enenflash/YounglingSlayer/mechanical design/metro/fusion.png

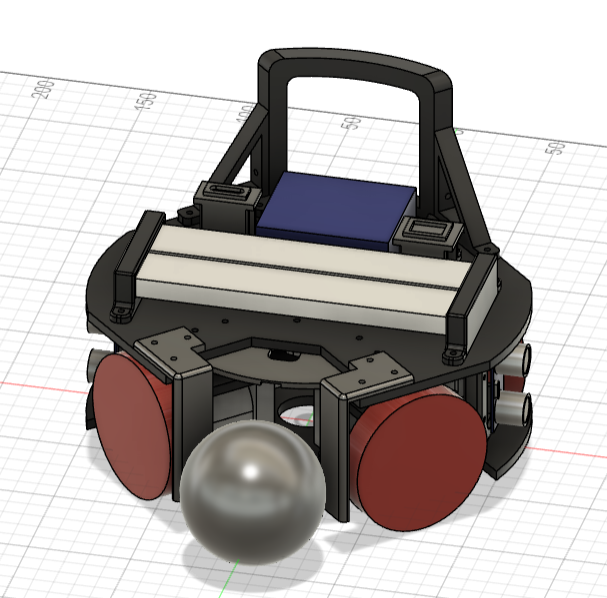
mechanical design/metro/fusion.png
