enenflash/YounglingSlayer/mechanical design/metro/L2_motor_mounts.png

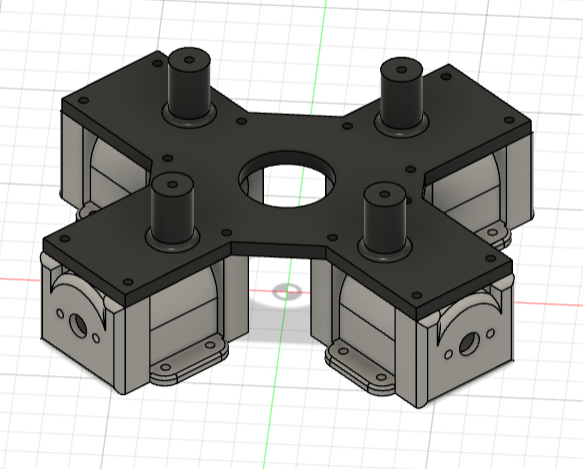
mechanical design/metro/L2_motor_mounts.png
