enenflash/YounglingSlayer/mechanical design/metro/L3_holes.png

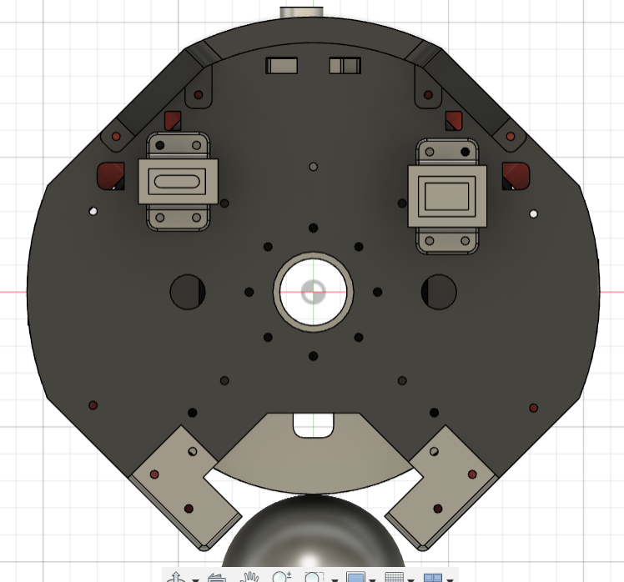
mechanical design/metro/L3_holes.png
