enenflash/YounglingSlayer/mechanical design/metro/layout.png

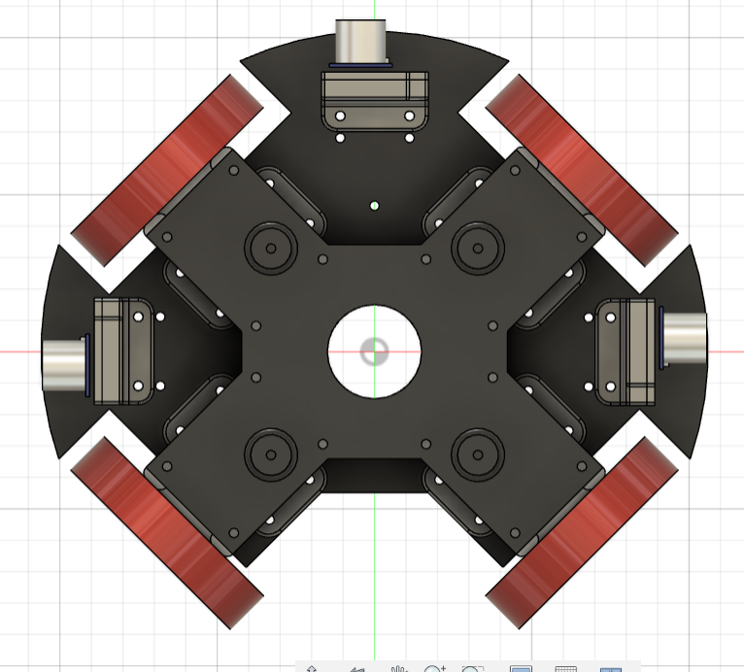
mechanical design/metro/layout.png
