enenflash/YounglingSlayer/mechanical design/metro/planning.png

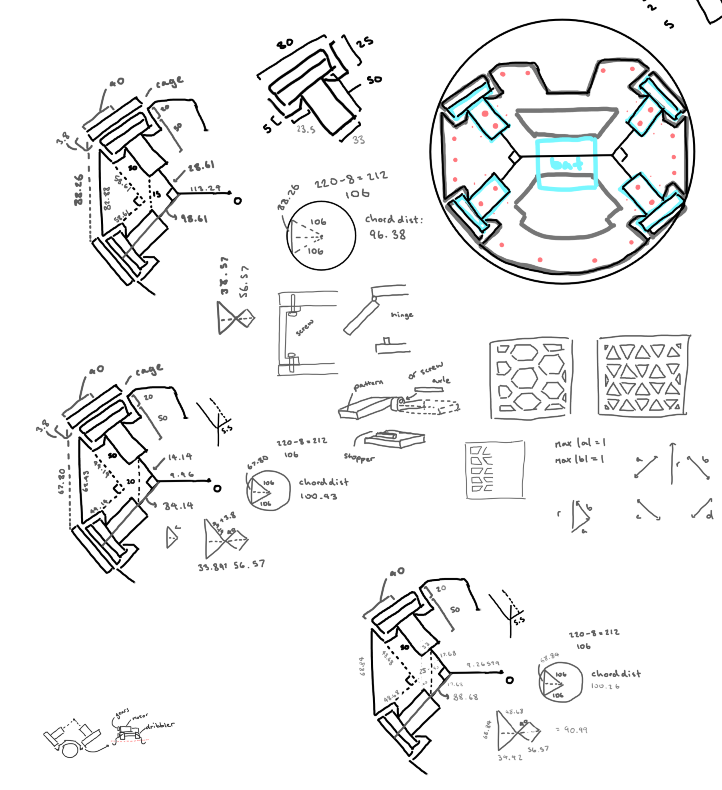
mechanical design/metro/planning.png
