enenflash/YounglingSlayer/mechanical design/metro/wheel/fusion.png

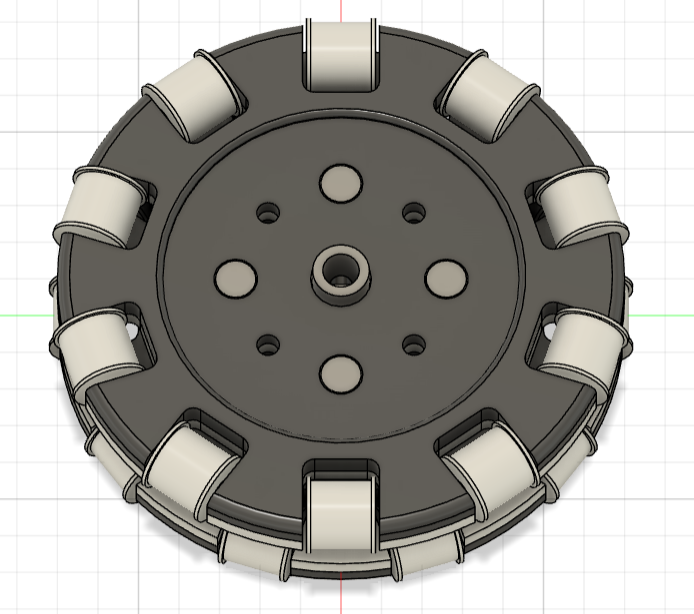
mechanical design/metro/wheel/fusion.png
