enenflash/YounglingSlayer/mechanical design/nationals/fusion.png

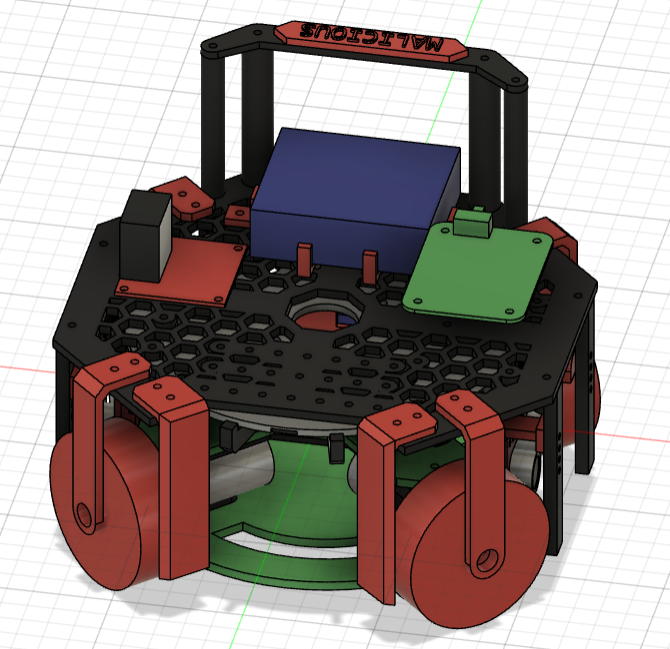
mechanical design/nationals/fusion.png
