enenflash/YounglingSlayer/mechanical design/nationals/wheel_guard.png

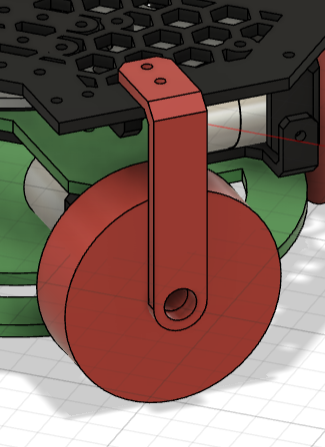
mechanical design/nationals/wheel_guard.png
