enenflash/YounglingSlayer/mechanical design/state/bottom_view.png

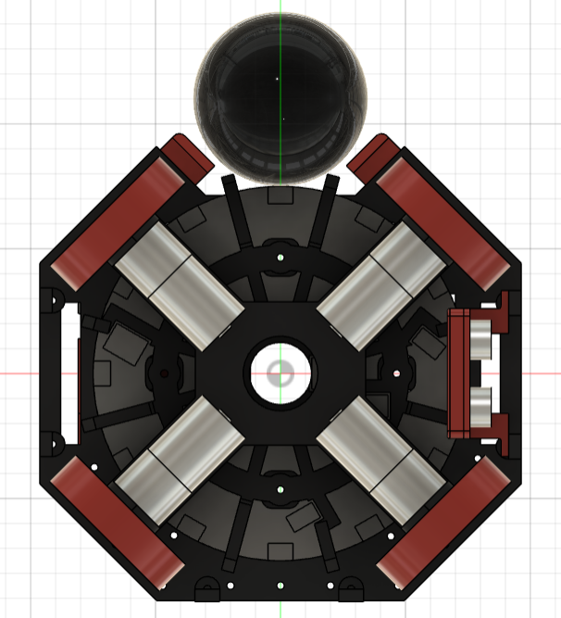
mechanical design/state/bottom_view.png
