enenflash/YounglingSlayer/mechanical design/state/fusion.png

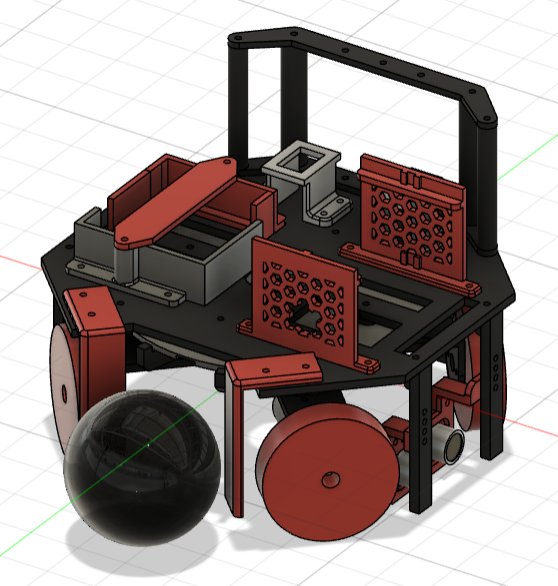
mechanical design/state/fusion.png
