enenflash/YounglingSlayer/mechanical design/state/IR_mount.png

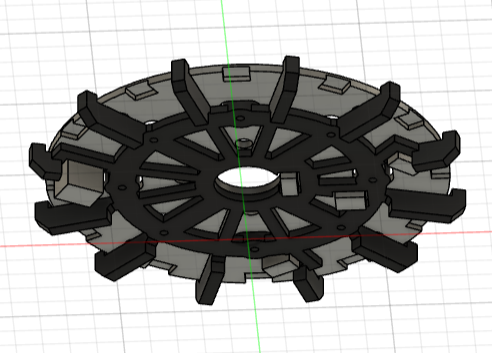
mechanical design/state/IR_mount.png
