enenflash/YounglingSlayer/mechanical design/state/L2-motors.png

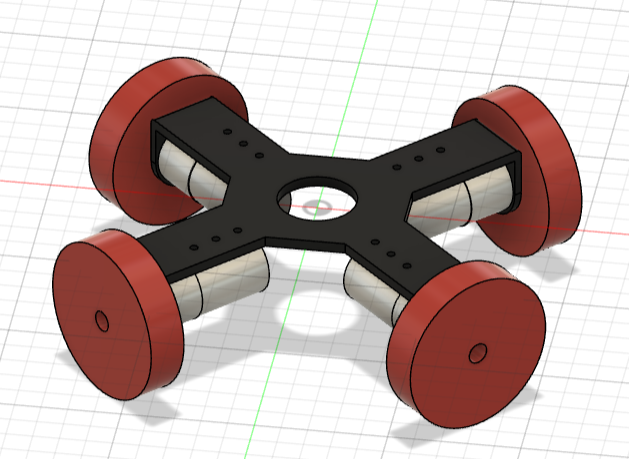
mechanical design/state/L2-motors.png
