enenflash/YounglingSlayer/mechanical design/state/structure.png

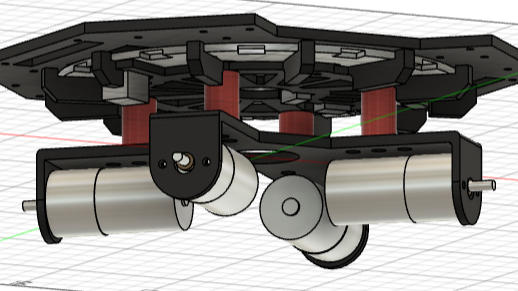
mechanical design/state/structure.png
