enenflash/YounglingSlayer/pcbs/line_sensor-26-08/design.png

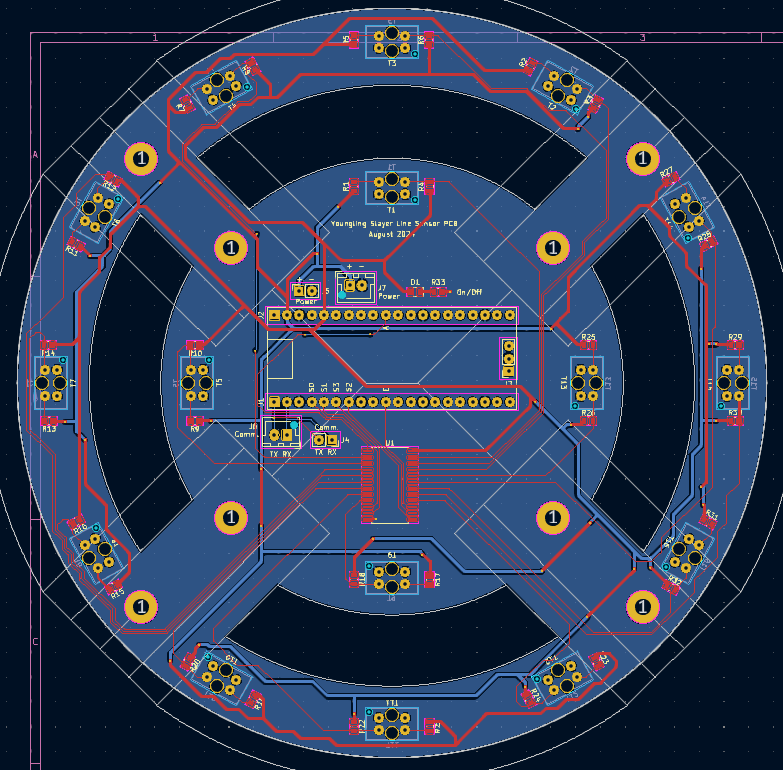
pcbs/line_sensor-26-08/design.png
