enenflash/YounglingSlayer/pcbs/line_sensor-26-08/down_3d_view.png

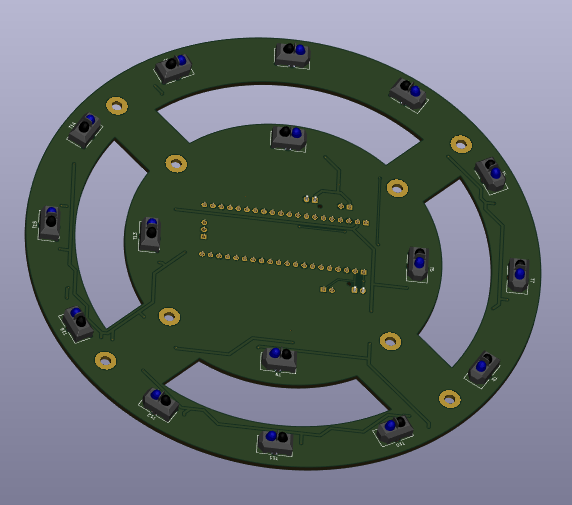
pcbs/line_sensor-26-08/down_3d_view.png
