enenflash/YounglingSlayer/pcbs/line_sensor-26-08/top_3d_view.png

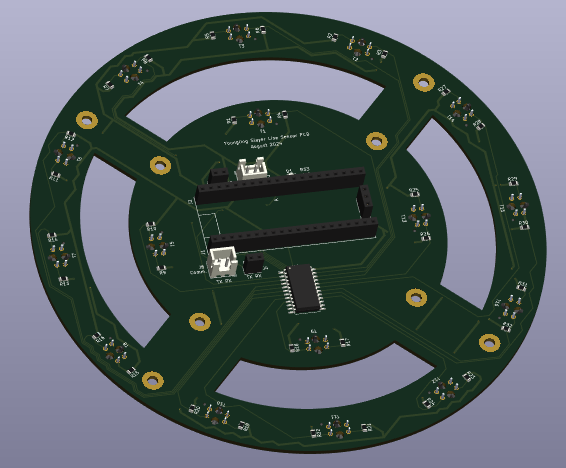
pcbs/line_sensor-26-08/top_3d_view.png
