enenflash/YounglingSlayer/pcbs/main_pcb_bottom/3d_view.png

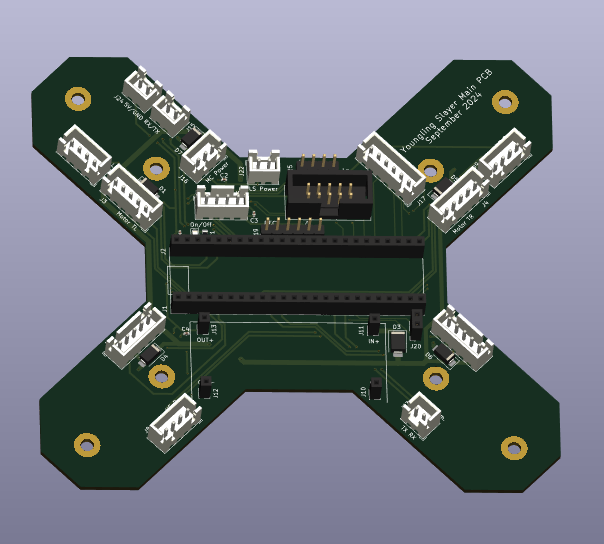
pcbs/main_pcb_bottom/3d_view.png
