enenflash/YounglingSlayer/pcbs/main_pcb_bottom/design.png

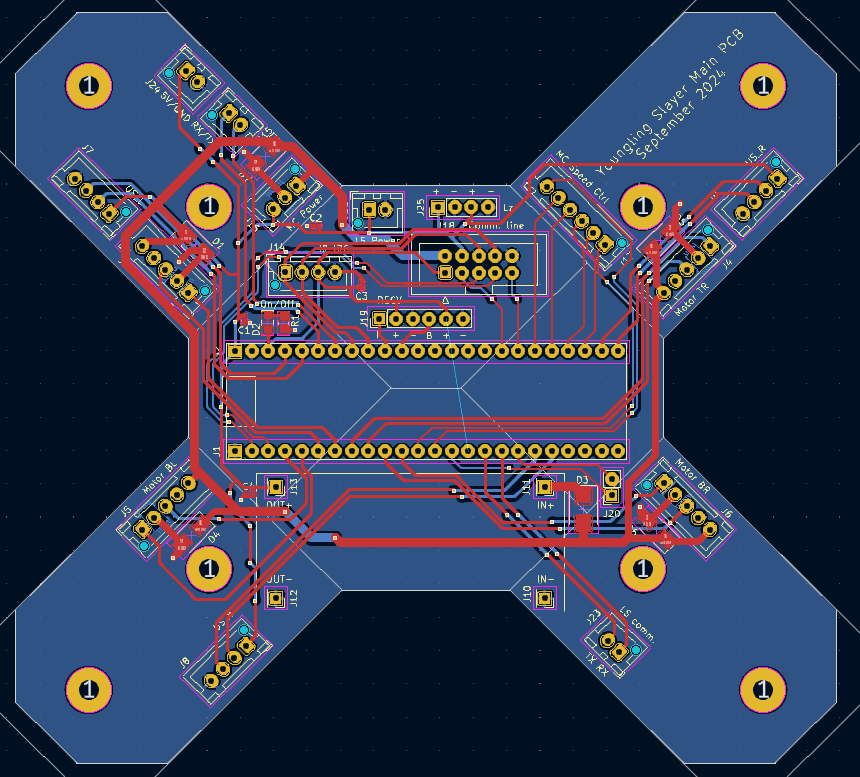
pcbs/main_pcb_bottom/design.png
