enenflash/YounglingSlayer/pcbs/main_pcb_bottom/schematic.png

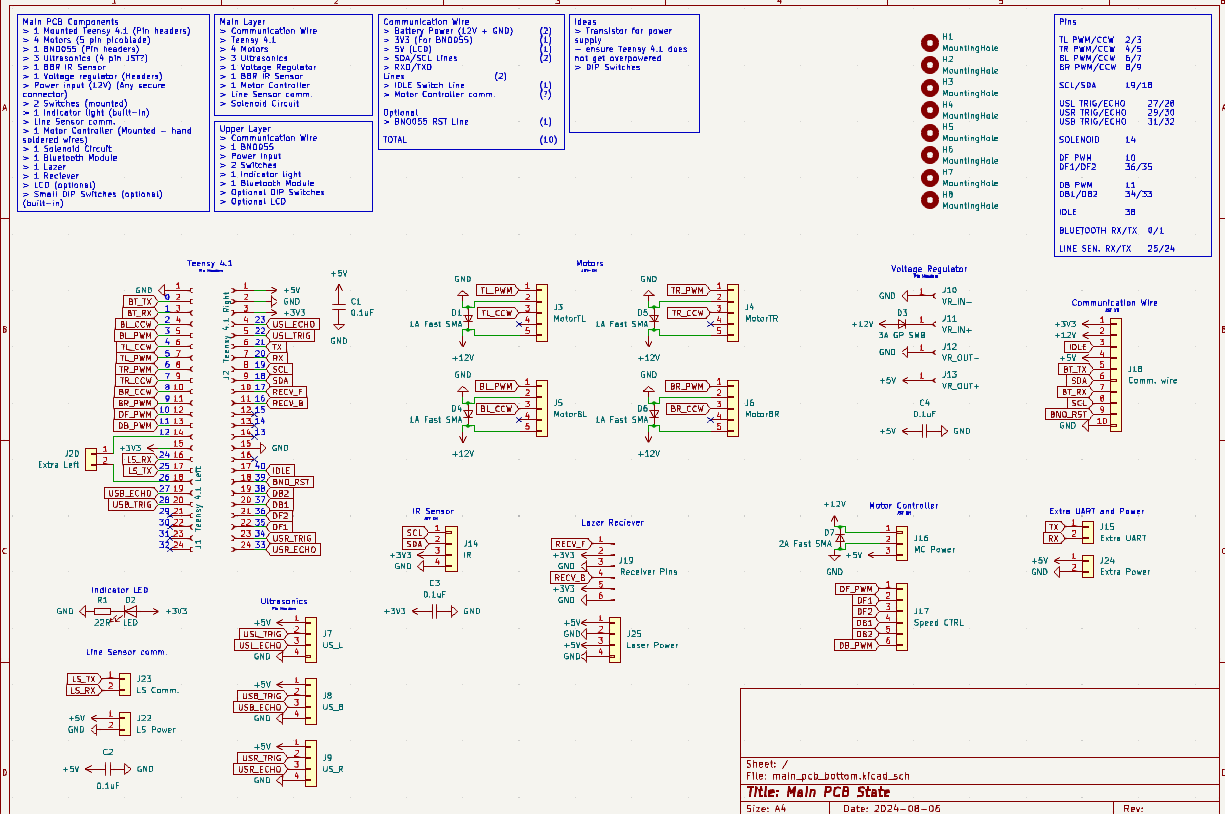
pcbs/main_pcb_bottom/schematic.png
