enenflash/YounglingSlayer/pcbs/main_pcb_top/3d_view.png

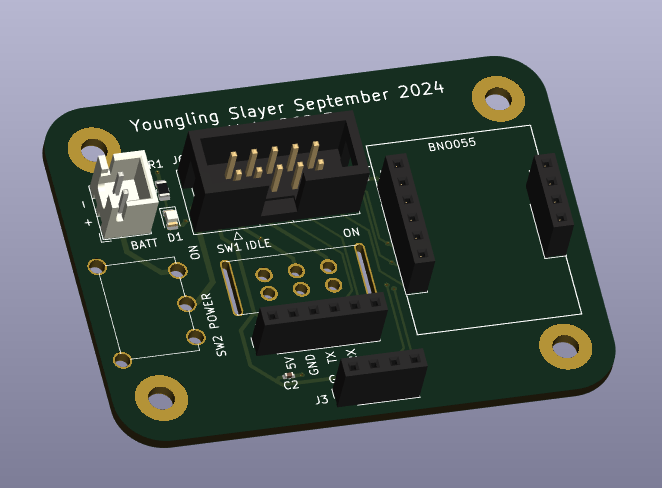
pcbs/main_pcb_top/3d_view.png
