enenflash/YounglingSlayer/pcbs/main_pcb_top/design.png

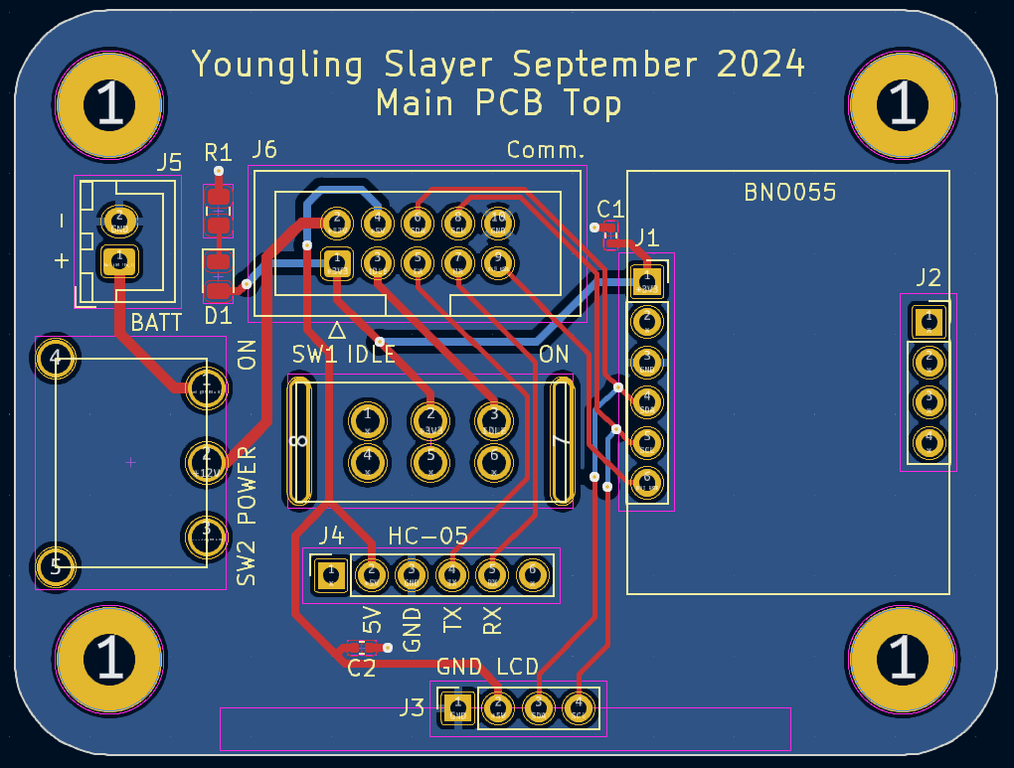
pcbs/main_pcb_top/design.png
