enenflash/YounglingSlayer/pcbs/main_pcb_top/schematic.png

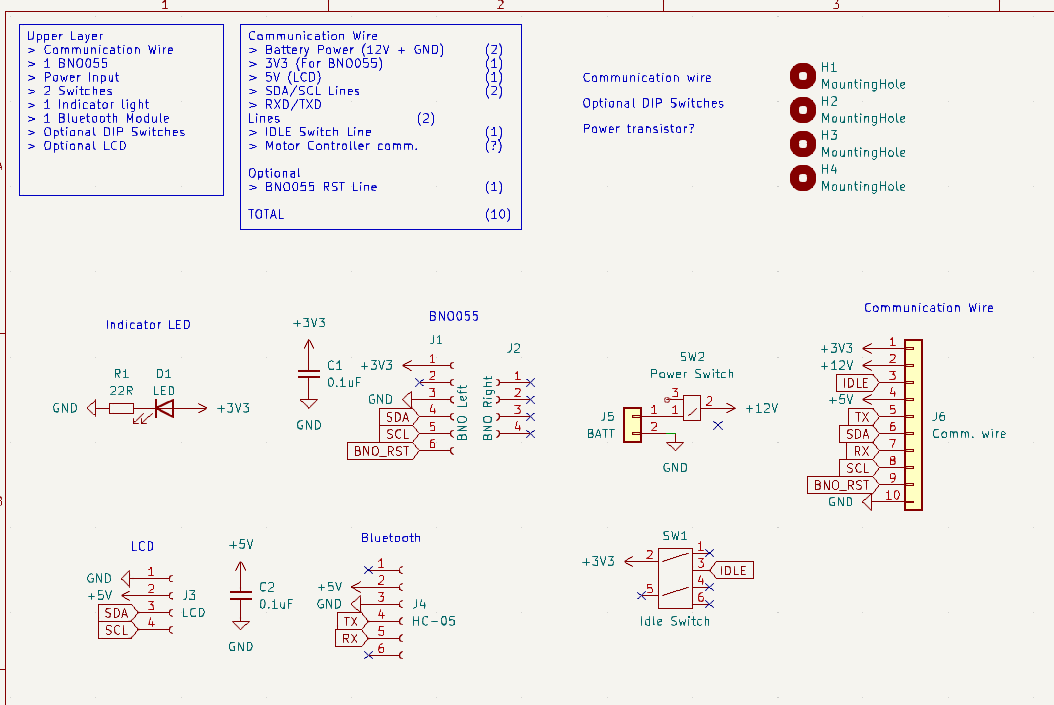
pcbs/main_pcb_top/schematic.png
