enenflash/YounglingSlayer/code-2024/nationals/RobotClass-goaltilt-1-10/RobotClass-goaltilt-1-10.ino

#include <iostream>
#include <array>
#include <map>
#include <algorithm>

#include <Wire.h>
#include <Adafruit_Sensor.h>
#include <Adafruit_BNO055.h>
#include <utility/imumaths.h>
#include <SoftwareSerial.h>

using namespace std;

// Motor Pins
#define TL_PWM 5
#define TL_DIR 4
#define TR_PWM 6
#define TR_DIR 7
#define BL_PWM 3
#define BL_DIR 2
#define BR_PWM 9
#define BR_DIR 8

// Ultrasonic Pins
#define USR_TRIG 34
#define USR_ECHO 33
#define USL_TRIG 22
#define USL_ECHO 23
#define USB_TRIG 28
#define USB_ECHO 27

// IDLE SWITCH
#define IDLE_PIN 40

#define FIELD_WIDTH 182
#define FIELD_LENGTH 243

// History lengths
const int DIR_HIST_LENGTH = 5;
const int STR_HIST_LENGTH = 5;
const int ULT_HIST_LENGTH = 5;

// Strength distances
const int RTB_SIDE = 15;
const int RTB_SIDE_EXTRA = 20;
const int RTB_BACK = 12;
const int ULTRASONIC_TO_ROBOT = 10;
const int SLOW_DOWN_STRENGTH = 30;

// Positions
const int GOAL_DEFENCE_Y = 220;
const int GOAL_POS_X = FIELD_WIDTH/2;
const int GOAL_POS_Y = 50;

// Ranges
const int TILT_RANGE = 10;
const int ULT_RANGE = 5;
const int GOAL_RANGE = 15;
const int GOAL_TILT_BOUND = 23;
const int TEAM_STRENGTH_DIFFERANCE = 10;

// Speeds
const int BALL_SIDE_SPEED = 80;
const int BALL_BEHIND_SPEED = 60; // note robot doesn't slow down at 3 and 9
const int LINE_SPEED = 20;

// IR direction to radians
std::map<int, float> irAngles = {
  { 0,  0        },
  { 11, PI/3     },
  { 10, PI/6     },
  { 9,  0        },
  { 8,  11*PI/6  },
  { 7,  5*PI/3   },
  { 6,  3*PI/2   },
  { 5,  4*PI/3   },
  { 4,  7*PI/6   },
  { 3,  PI       },
  { 2,  5*PI/6   },
  { 1,  2*PI/3   },
  { 12, PI/2     }
};
