enenflash/YounglingSlayer/code-2024/nationals/Final-Nationals-20-10/ultrasonic.ino

// ultrasonic class
class Ultrasonic {
public:
  int trigger_pin;
  int echo_pin;

  Ultrasonic(int TRIGGER_PIN, int ECHO_PIN) {
    trigger_pin = TRIGGER_PIN;
    echo_pin = ECHO_PIN;
  }

  // getting distance from ultrasonic
  int getDistance() {
    long duration, ult_distance;

    // clear trigger pin
    digitalWrite(trigger_pin, LOW);
    delayMicroseconds(2);
    digitalWrite(trigger_pin, HIGH);
    delayMicroseconds(10);
    digitalWrite(trigger_pin, LOW);

    // get duration in miliseconds
    duration = pulseIn(echo_pin, HIGH, 20000);
    
    // converet to cm
    ult_distance = (duration / 29) / 2;  // Calculating the ult_distance

    return ult_distance;
  }
};

// class to create grid system of field
class PositionSystem {
private:
  Ultrasonic ultLeft = Ultrasonic(USL_TRIG, USL_ECHO);
  Ultrasonic ultRight = Ultrasonic(USR_TRIG, USR_ECHO);
  Ultrasonic ultBack = Ultrasonic(USB_TRIG, USB_ECHO);

  // LEFT, RIGHT, BACK
  int rawDistances[3] = {0};
  float trueDistances[3] = {0};
  float previousDistances[3] = {0};

  float deltaDistances[3] = {0};

  void getRawDistances() {
    rawDistances[0] = ultLeft.getDistance() + ULTRASONIC_TO_ROBOT;
    rawDistances[1] = ultRight.getDistance() + ULTRASONIC_TO_ROBOT;
    rawDistances[2] = ultBack.getDistance() + ULTRASONIC_TO_ROBOT;
  };

  void getTrueDistances(float tilt) { // tilt in radians
    for (int i = 0; i < 3; i++) {
      trueDistances[i] = cos(tilt)*rawDistances[i];
    }

    if (trueDistances[0] > 75 && trueDistances[1] < 100) {
        trueDistances[0] += 30;
    }
    else if (trueDistances[1] > 75 && trueDistances[0] < 100) {
      trueDistances[1] += 30;
    }
    else if (trueDistances[0] + trueDistances[1] < 130) {
      trueDistances[0] += 30;
      trueDistances[1] += 30;
    }
  };

  bool totalWidthCompare() {
    return abs((trueDistances[0]+trueDistances[1])-FIELD_WIDTH) < 20;
  };

  void getDeltaDistances() {
    for (int i = 0; i < 3; i++) {
      deltaDistances[i] = abs(trueDistances[i]-previousDistances[i]);
    }
  };

  void logPreviousDistances() {
    for (int i = 0; i < 3; i++) {
      previousDistances[i] = trueDistances[i];
    }
  };

public:
  bool reliable = true;
  int usingIndex = 0; 

  float x, y;
  void chooseULT() {
    getDeltaDistances();

    if (deltaDistances[0] > 20 && deltaDistances[1] > 20) {
      usingIndex = 0;
      reliable = false;
    }
    else if (deltaDistances[0] > 20) {
      usingIndex = 1;
      reliable = true;
    }
    else if (deltaDistances[1] > 20) {
      usingIndex = 0;
      reliable = true;
    }
    else {
      usingIndex = 0;
      reliable = true;
    }
  };

  // update ultrasonics and position system
  void update(float tilt) {
    getRawDistances();
    getTrueDistances(tilt);

    if (!totalWidthCompare()) {
      Serial.println("Choose ULT");
      chooseULT();
    }
    
    if (usingIndex == 0) {
      x = trueDistances[0];
    }
    else if (usingIndex == 1) {
      x = FIELD_WIDTH - trueDistances[1];
    }

    y = FIELD_LENGTH - trueDistances[2];

    if (totalWidthCompare()) {
      logPreviousDistances();
    }
  };

  // debugging
  void serialPrint() {
    Serial.print("TrueLeft: ");
    Serial.print(trueDistances[0]);
    Serial.print(" TrueRight: ");
    Serial.println(trueDistances[1]);

    Serial.print("Reliable: ");
    Serial.print(reliable);
    Serial.print(" usingIndex: ");
    Serial.println(usingIndex);
  }
};
