enenflash/YounglingSlayer/code-2024/nationals/Final-Nationals-20-10/ir.ino

// ir sensor class
class IRSensor {
private:
  // variable initilisations
  int strength;
  int direction;
  int dirHistory[DIR_HIST_LENGTH] = {12, 12, 12, 12, 12};
  int strHistory[STR_HIST_LENGTH] = {40, 40, 40, 40, 40};

  // histories for greater accuracy
  void updateStrHistory() {
    for (int i = 0; i < STR_HIST_LENGTH; i++) {
      if (i != STR_HIST_LENGTH-1) {
        strHistory[i] = strHistory[i+1];
      }
      else {
        strHistory[i] = strength;
      }
    }
  };

  void updateDirHistory() {
    for (int i = 0; i < DIR_HIST_LENGTH; i++) {
      if (i != DIR_HIST_LENGTH-1) {
        dirHistory[i] = dirHistory[i+1];
      }
      else {
        dirHistory[i] = direction;
      }
    }
  };

  // finds the most occuring IR reading from a history of directions
  int mostCommonDirection() {
    int directionCount[13] = {0};
    
    for (int i = 0; i < DIR_HIST_LENGTH; i++) {
      directionCount[dirHistory[i]]++;
    }
    
    int count = directionCount[dirHistory[DIR_HIST_LENGTH-1]];
    int direction = dirHistory[DIR_HIST_LENGTH-1];
    
    for (int i = 0; i < 13; i++) {
      if (directionCount[i] > count) {
        count = directionCount[i];
        direction = i;
      }
    }
    return direction;
  };

public:
  // reading data from ir sensor
  void readData() {
    Wire.requestFrom(0x08, 2);
    if (Wire.available()) {
      direction = Wire.read();
      strength = Wire.read();
    }

    // updating histories
    updateDirHistory();
    updateStrHistory();
  };

  int getRawDirection() {
    return direction;
  };

  int getRawStrength() {
    return strength;
  };

  // filtering direction using history and most common values
  int getFilteredDirection() {
    return mostCommonDirection();
  };

  // fitering strength by finding average
  int getFilteredStrength() {
    int totalStrength = 0;
    for (int i = 0; i < STR_HIST_LENGTH; i++) {
      totalStrength += strHistory[i];
    }
    return totalStrength / (STR_HIST_LENGTH + 0.0);
  };
};
