enenflash/YounglingSlayer/code-2024/states/code_v1 Final State Code/constant_variables.ino

const int ROBOT_TO_BALL = 9;
const int ROBOT_TO_BALL_MULTIPLY = 2;
const int FIELD_WIDTH = 182;
const int FIELD_HEIGHT = 243;
const int ULTRASONIC_TO_ROBOT = 11;

// hard coded ir_angles values
std::map<int, int> ir_angles = {
  { 0, 0 },
  { 11, 60},
  { 10, 30 },
  { 9, 0 },
  { 8, 330 },
  { 7, 300 },
  { 6, 270 },
  { 5, 240 },
  { 4, 210 },
  { 3, 180 },
  { 2, 150 },
  { 1, 120 },
  { 12, 90 }
};
