enenflash/YounglingSlayer/code-2024/test code/LCD_Testing.ino

/**********************************************************************
  Filename    : Drive LiquidCrystal I2C to display characters
  Description : I2C is used to control the display characters of LCD1602.
  Auther      : www.freenove.com
  Modification: 2022/06/28
**********************************************************************/
#include <LiquidCrystal_I2C.h>

// initialize the library with the numbers of the interface pins
LiquidCrystal_I2C lcd(0x3F, 16, 2);

void setup() {
  lcd.init();                // initialize the lcd
  lcd.backlight();           // Turn on backlight
  lcd.print("hello, world!");// Print a message to the LCD
  
}

void loop() {
  // (note: line 1 is the second row, since counting begins with 0):
  lcd.setCursor(0, 1);// set the cursor to column 0, line 1
  // print the number of seconds since reset:
  lcd.print("Counter:");
  lcd.print(millis() / 1000);
  
}

bool i2CAddrTest(uint8_t addr) {
  Wire.begin();
  Wire.beginTransmission(addr);
  if (Wire.endTransmission() == 0) {
    return true;
  }
  return false;
}
